satlab/bluebox/software/firmware/Descriptors.c

/*
 * Copyright (c) 2012 Jeppe Ledet-Pedersen <jlp@satlab.org>
 *
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
 * THE SOFTWARE IS PROVIDED "AS IS", WITHOUT WARRANTY OF ANY KIND, EXPRESS OR
 * IMPLIED, INCLUDING BUT NOT LIMITED TO THE WARRANTIES OF MERCHANTABILITY,
 * FITNESS FOR A PARTICULAR PURPOSE AND NONINFRINGEMENT. IN NO EVENT SHALL THE
 * AUTHORS OR COPYRIGHT HOLDERS BE LIABLE FOR ANY CLAIM, DAMAGES OR OTHER
 * LIABILITY, WHETHER IN AN ACTION OF CONTRACT, TORT OR OTHERWISE, ARISING FROM,
 * OUT OF OR IN CONNECTION WITH THE SOFTWARE OR THE USE OR OTHER DEALINGS IN
 * THE SOFTWARE.
 */

#include <avr/eeprom.h>

#include "Descriptors.h"
#include "bluebox.h"

const USB_Descriptor_Device_t PROGMEM BlueBox_DeviceDescriptor = {
	.Header                 = {.Size = sizeof(USB_Descriptor_Device_t), .Type = DTYPE_Device},

	.USBSpecification       = VERSION_BCD(01.10),
	.Class                  = USB_CSCP_VendorSpecificClass,
	.SubClass               = USB_CSCP_NoDeviceSubclass,
	.Protocol               = USB_CSCP_NoDeviceProtocol,

	.Endpoint0Size          = FIXED_CONTROL_ENDPOINT_SIZE,

	.VendorID               = 0x1d50,
	.ProductID              = 0x6054,

	.ReleaseNumber          = VERSION_BCD(01.00),

	.ManufacturerStrIndex   = 0x01,
	.ProductStrIndex        = 0x02,
	.SerialNumStrIndex      = 0x03,

	.NumberOfConfigurations = FIXED_NUM_CONFIGURATIONS
};

const USB_Descriptor_Configuration_t PROGMEM BlueBox_ConfigurationDescriptor =
{
	.Config = {
		.Header                 = {.Size = sizeof(USB_Descriptor_Configuration_Header_t), .Type = DTYPE_Configuration},

		.TotalConfigurationSize = sizeof(USB_Descriptor_Configuration_t),
		.TotalInterfaces        = 1,
		.ConfigurationNumber    = 1,
		.ConfigurationStrIndex  = NO_DESCRIPTOR,
		.ConfigAttributes       = USB_CONFIG_ATTR_RESERVED,
		.MaxPowerConsumption    = USB_CONFIG_POWER_MA(500)
	},

	.Interface = {
		.Header                 = {.Size = sizeof(USB_Descriptor_Interface_t), .Type = DTYPE_Interface},

		.InterfaceNumber        = 0,
		.AlternateSetting       = 0,
		.TotalEndpoints         = 2,
		.Class                  = USB_CSCP_VendorSpecificClass,
		.SubClass               = 0x00,
		.Protocol               = 0x00,
		.InterfaceStrIndex      = NO_DESCRIPTOR
	},

	.DataInEndpoint = {
		.Header                 = {.Size = sizeof(USB_Descriptor_Endpoint_t), .Type = DTYPE_Endpoint},

		.EndpointAddress        = IN_EPADDR,
		.Attributes             = (EP_TYPE_INTERRUPT | ENDPOINT_ATTR_NO_SYNC | ENDPOINT_USAGE_DATA),
		.EndpointSize           = IN_EPSIZE,
		.PollingIntervalMS      = 0x01,
	},

	.DataOutEndpoint = {
		.Header                 = {.Size = sizeof(USB_Descriptor_Endpoint_t), .Type = DTYPE_Endpoint},

		.EndpointAddress        = OUT_EPADDR,
		.Attributes             = (EP_TYPE_INTERRUPT | ENDPOINT_ATTR_NO_SYNC | ENDPOINT_USAGE_DATA),
		.EndpointSize           = OUT_EPSIZE,
		.PollingIntervalMS      = 0x01,
	},
};

const USB_Descriptor_String_t PROGMEM BlueBox_LanguageString = {
	.Header                 = {.Size = USB_STRING_LEN(1), .Type = DTYPE_String},
	.UnicodeString          = {LANGUAGE_ID_ENG}
};

const USB_Descriptor_String_t PROGMEM BlueBox_ManufacturerString = {
	.Header                 = {.Size = USB_STRING_LEN(14), .Type = DTYPE_String},
	.UnicodeString          = L"Satlab/AAUSAT3"
};

const USB_Descriptor_String_t PROGMEM BlueBox_ProductString = {
#if defined(BBSTANDARD)
	.Header                 = {.Size = USB_STRING_LEN(7), .Type = DTYPE_String},
	.UnicodeString          = L"BlueBox"
#elif defined(BBMICRO)
	.Header                 = {.Size = USB_STRING_LEN(13), .Type = DTYPE_String},
	.UnicodeString		= L"BlueBox Micro"
#endif
};

USB_Descriptor_String_t BlueBox_SerialString = {
	.Header                 = {.Size = USB_STRING_LEN(8), .Type = DTYPE_String},
	.UnicodeString          = L"00000000"
};

static void format_serial(uint32_t serial, uint16_t *output)
{
	int i;
	char sstr[9];

	snprintf(sstr, 9, "%08lx", serial);
	sstr[8] = '\0';

	for (i = 0; i < 8; i++)
		output[i] = cpu_to_le16(sstr[i]);

}

uint16_t CALLBACK_USB_GetDescriptor(const uint16_t wValue,
				    const uint8_t wIndex,
				    const void **const DescriptorAddress,
				    uint8_t *DescriptorMemorySpace)
{
	uint32_t snum;
	const uint8_t DescriptorType   = (wValue >> 8);
	const uint8_t DescriptorNumber = (wValue & 0xFF);

	const void *Address = NULL;
	uint16_t Size = NO_DESCRIPTOR;

	*DescriptorMemorySpace = MEMSPACE_FLASH;

	switch (DescriptorType) {
	case DTYPE_Device:
		Address = &BlueBox_DeviceDescriptor;
		Size    = sizeof(USB_Descriptor_Device_t);
		break;
	case DTYPE_Configuration:
		Address = &BlueBox_ConfigurationDescriptor;
		Size    = sizeof(USB_Descriptor_Configuration_t);
		break;
	case DTYPE_String:
		switch (DescriptorNumber)
		{
			case 0x00:
				Address = &BlueBox_LanguageString;
				Size    = pgm_read_byte(&BlueBox_LanguageString.Header.Size);
				break;
			case 0x01:
				Address = &BlueBox_ManufacturerString;
				Size    = pgm_read_byte(&BlueBox_ManufacturerString.Header.Size);
				break;
			case 0x02:
				Address = &BlueBox_ProductString;
				Size    = pgm_read_byte(&BlueBox_ProductString.Header.Size);
				break;
			case 0x03:
				Address = &BlueBox_SerialString;
				Size    = BlueBox_SerialString.Header.Size;

				snum = eeprom_read_dword(&serialno);
				format_serial(snum, ((uint16_t *) &BlueBox_SerialString.UnicodeString));

				*DescriptorMemorySpace = MEMSPACE_RAM;
				break;
		}

		break;
	}

	*DescriptorAddress = Address;
	return Size;
}

void EVENT_USB_Device_ConfigurationChanged(void)
{
	Endpoint_ConfigureEndpoint(IN_EPADDR,  EP_TYPE_INTERRUPT, IN_EPSIZE,  1);
	Endpoint_ConfigureEndpoint(OUT_EPADDR, EP_TYPE_INTERRUPT, OUT_EPSIZE, 1);
}
